zainul511/Flood-Risk-Monitoring-Assessment-System/Hardware/controller_unit/docs/controller_unit_3d.jpg

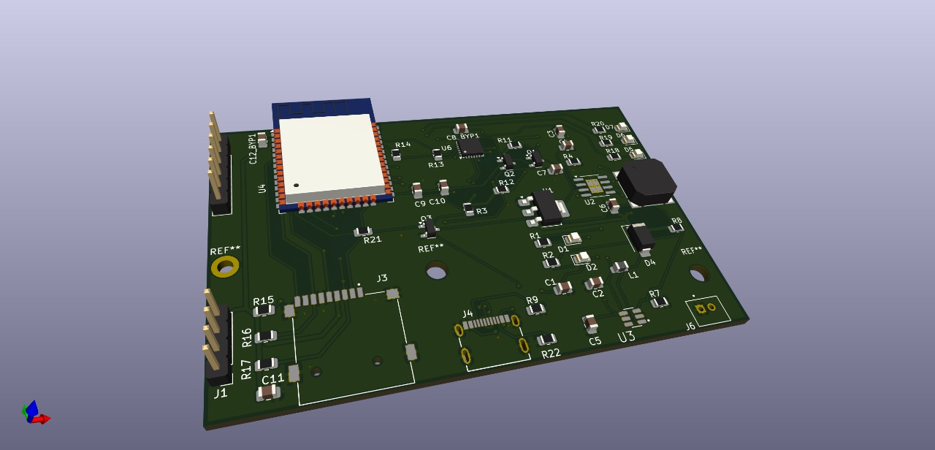
Hardware/controller_unit/docs/controller_unit_3d.jpg
