zainul511/Flood-Risk-Monitoring-Assessment-System/Hardware/controller_unit/docs/controller_unitschematic_page-0002.jpg

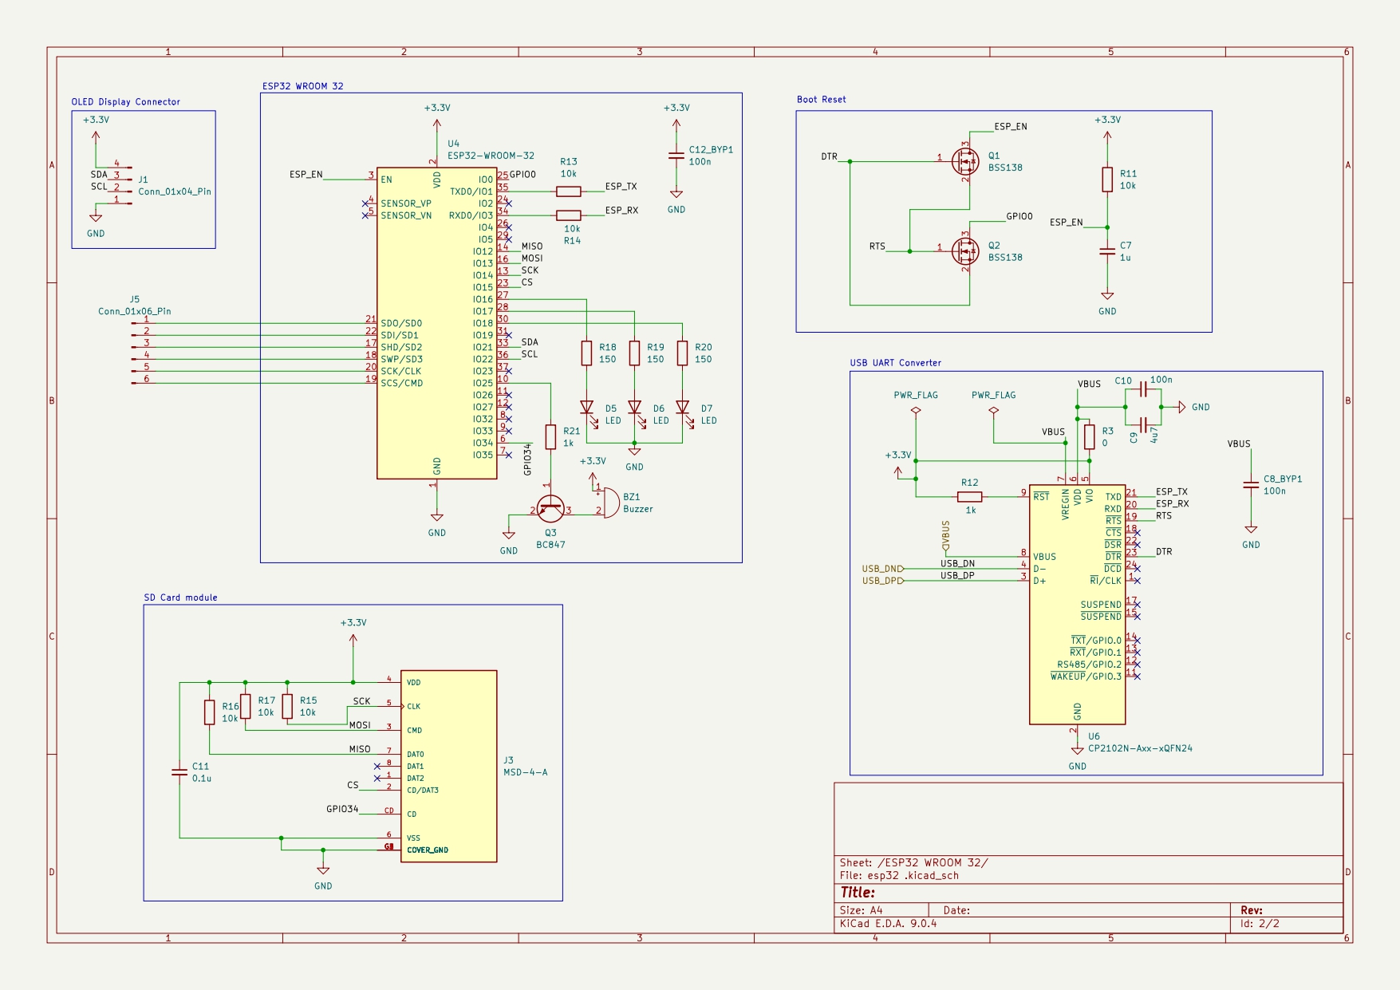
Hardware/controller_unit/docs/controller_unitschematic_page-0002.jpg
