zainul511/Flood-Risk-Monitoring-Assessment-System/Hardware/data-unit/docs/data-unit_board.jpg

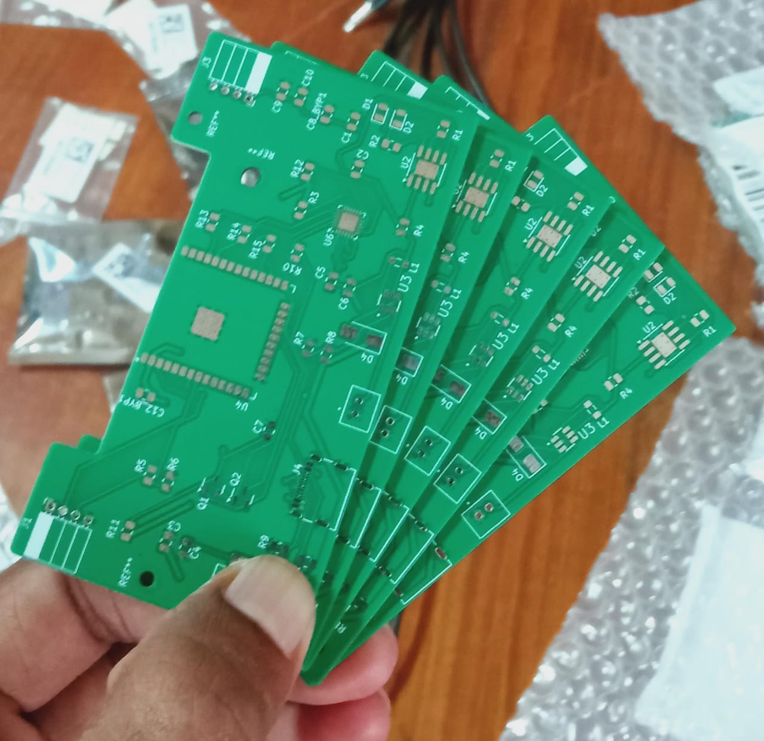
Hardware/data-unit/docs/data-unit_board.jpg
