zainul511/Flood-Risk-Monitoring-Assessment-System/Images/controller_unit_pcb.jpeg

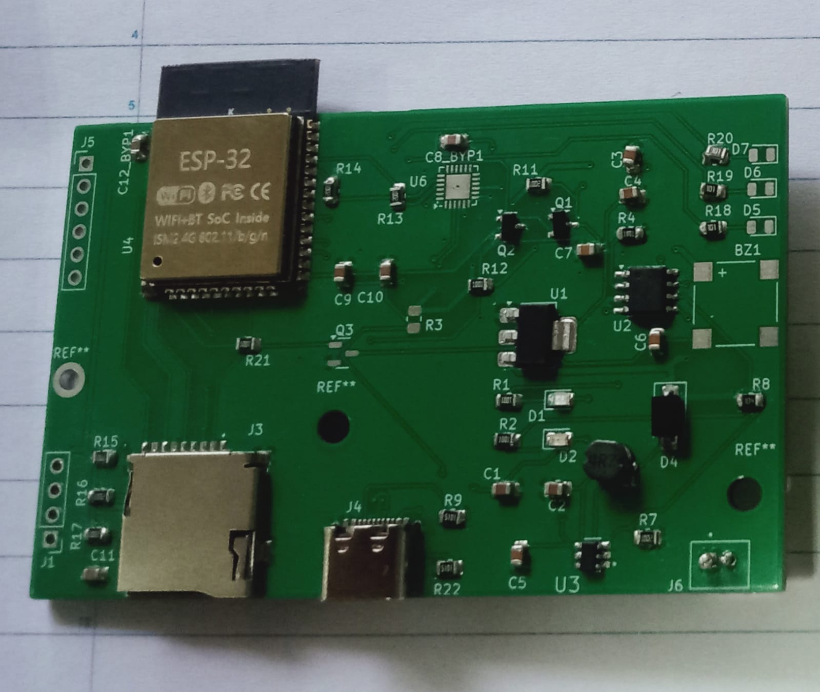
Images/controller_unit_pcb.jpeg
