zainul511/Flood-Risk-Monitoring-Assessment-System/Images/dashboard_view.jpeg

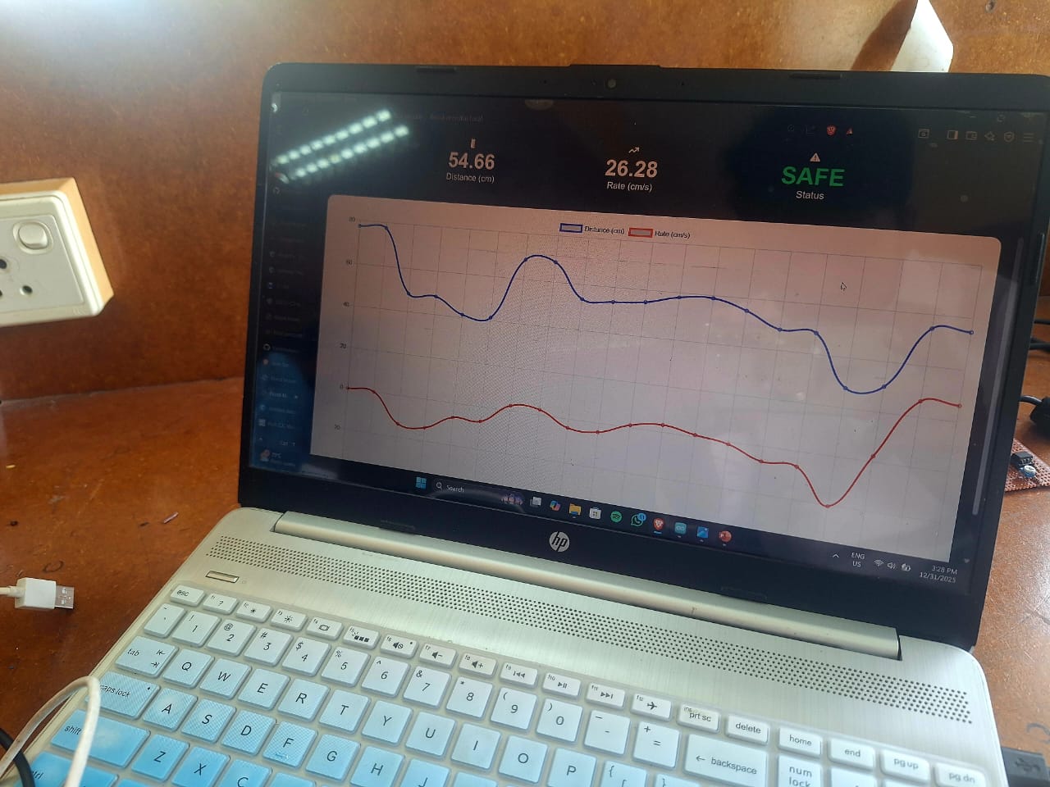
Images/dashboard_view.jpeg
