zainul511/Flood-Risk-Monitoring-Assessment-System/Images/data-unit_pcb.jpeg

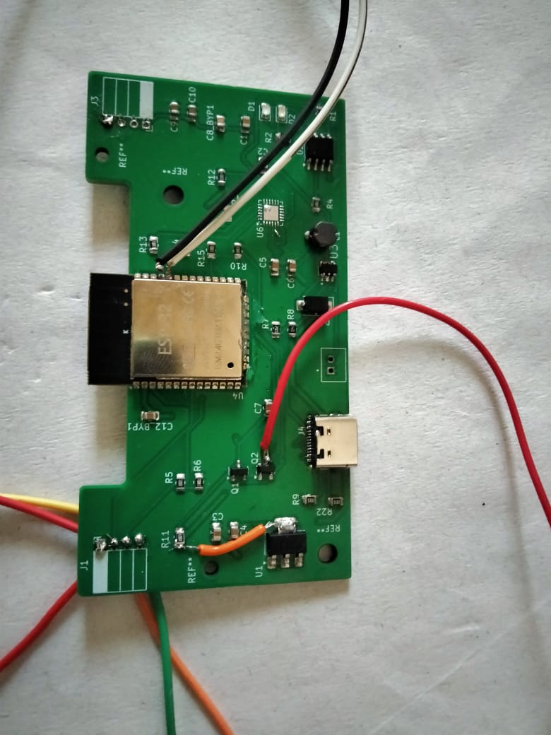
Images/data-unit_pcb.jpeg
