zainul511/Flood-Risk-Monitoring-Assessment-System/Images/data_unit1_pcb.jpeg

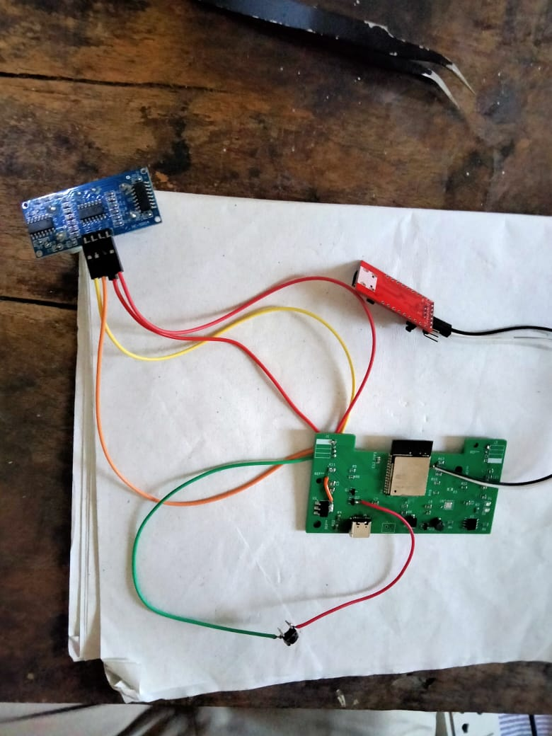
Images/data_unit1_pcb.jpeg
