zainul511/Flood-Risk-Monitoring-Assessment-System/Images/system_demo.jpeg

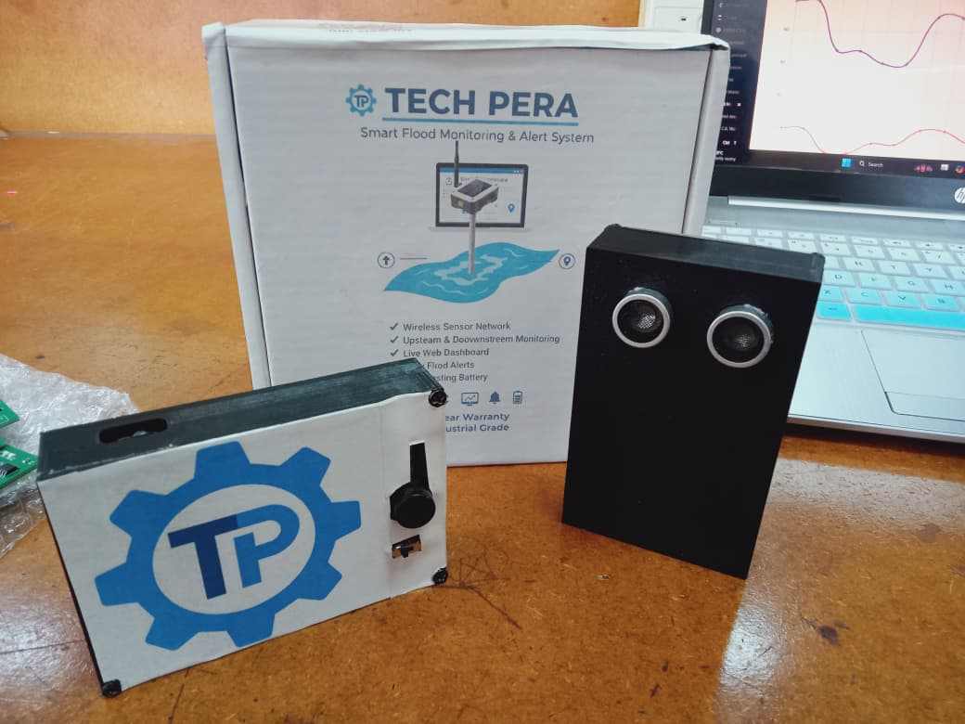
Images/system_demo.jpeg
